salehjg/AINGF2/FPGA_Side/ipcore_dir/icon1.v

///////////////////////////////////////////////////////////////////////////////
// Copyright (c) 2015 Xilinx, Inc.
// All Rights Reserved
///////////////////////////////////////////////////////////////////////////////
//   ____  ____
//  /   /\/   /
// /___/  \  /    Vendor     : Xilinx
// \   \   \/     Version    : 14.7
//  \   \         Application: Xilinx CORE Generator
//  /   /         Filename   : icon1.v
// /___/   /\     Timestamp  : Wed Nov 25 22:33:35 Iran Standard Time 2015
// \   \  /  \
//  \___\/\___\
//
// Design Name: Verilog Synthesis Wrapper
///////////////////////////////////////////////////////////////////////////////
// This wrapper is used to integrate with Project Navigator and PlanAhead

`timescale 1ns/1ps

module icon1(
    CONTROL0) /* synthesis syn_black_box syn_noprune=1 */;


inout [35 : 0] CONTROL0;

endmodule
