salehjg/AINGF2/FPGA_Side/ipcore_dir/ila1/example_design/example_ila1.v

//////////////////////////////////////////////////////////////////////////////
//$Date: 2012/02/06 10:34:16 $
//$RCSfile: example_design.ejava,v $
//$Revision: 1.4 $
///////////////////////////////////////////////////////////////////////////////
//   ____  ____ 
//  /   /\/   /
// /___/  \  /    Vendor: Xilinx
// \   \   \/     Version : 1.05
//  \   \         Application : ILA V1.05a
//  /   /         Filename : example_ila1.v
// /___/   /\     
// \   \  /  \ 
//  \___\/\___\
//
// (c) Copyright 2010 Xilinx, Inc. All rights reserved.
// 
// This file contains confidential and proprietary information
// of Xilinx, Inc. and is protected under U.S. and
// international copyright and other intellectual property
// laws.
// 
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
// CRITICAL APPLICATIONS
// Xilinx products are not designed or intended to be fail-
// safe, or for use in any application requiring fail-safe
// performance, such as life-support or safety devices or
// systems, Class III medical devices, nuclear facilities,
// applications related to the deployment of airbags, or any
// other applications that could lead to death, personal
// injury, or severe property or environmental damage
// (individually and collectively, "Critical
// Applications"). Customer assumes the sole risk and
// liability of any use of Xilinx products in Critical
// Applications, subject only to applicable laws and
// regulations governing limitations on product liability.
// 
// THIS COPYRIGHT NOTICE AND DISCLAIMER MUST BE RETAINED AS
// PART OF THIS FILE AT ALL TIMES.

`timescale 1ns / 1ps

//The example module here illustrates how ila core can be instantiated in
//a user design. This helps the user on how various ports selected for the core can be used.

module example_ila1
  (
 
    input         clk_i); 
  //****************************************************************************
  //  Local Parameters
  //****************************************************************************
  parameter C_NUM_OF_TRIGPORTS = 2;
  parameter C_TRIG0_SIZE = 20;
  parameter C_TRIG1_SIZE = 1;


  //****************************************************************************
  //  Local Signals
  //****************************************************************************
  wire clk;
  wire [35:0] control0;
  wire [C_TRIG0_SIZE-1:0] trig_0;
  wire [C_TRIG1_SIZE-1:0] trig_1;
  wire [C_NUM_OF_TRIGPORTS:0] en_out_int;


   
 
  BUFG bufg_inst
    (
      .O(clk),
      .I(clk_i));
  //-----------------------------------------------------------------
  //
  //  For TRIG0
  //
  //-----------------------------------------------------------------
  // This shift register takes enable_in and registers enable_out. Size of 
  // shift register is given as TRIG0 width. Output of shift register 
  // is mapped to TRIG0.en_out of this shift_reg instance can be used as
  // en_in for next shift_reg instance. 

  // Enabling First shift register

  assign en_out_int[0] = 1'b1;

  shift_reg
    #(.WIDTH(C_TRIG0_SIZE))
    U_SHIFT_REGISTER_0
      (
       .clk(clk),
       .en_in(en_out_int[0]),
       .en_out(en_out_int[1]),
       .shiftout(trig_0));

  //-----------------------------------------------------------------
  //
  //  For TRIG1
  //
  //-----------------------------------------------------------------
  // This shift register takes enable_in from the previous shift register and 
  // registers enable_out.Size of shift register is given as TRIG1 width.
  // Output of shift register is mapped TRIG1. en_out of this shift_reg 
  // instance can be used as en_in for next shift_reg instance.Each trigger port 
  // in the design can be distinguished by its pulse width.TRIG0 signals 
  // are of shorter width than those of TRIG1.

  shift_reg
    #(.WIDTH(C_TRIG1_SIZE))
    U_SHIFT_REGISTER_1
      (
       .clk(clk),
       .en_in(en_out_int[1]),
       .en_out(en_out_int[2]),
       .shiftout(trig_1));

  //-----------------------------------------------------------------
  //
  //  IF TRIGOUT Port is selected
  //
  //-----------------------------------------------------------------


  //-----------------------------------------------------------------
  //
  //  If Data not same as trigger
  //
  //-----------------------------------------------------------------

  //-----------------------------------------------------------------
  //
  //  ICON Pro core instance
  //
  //-----------------------------------------------------------------
  // Icon core is instantiated to connect to ILA core.
  chipscope_icon ICON_inst 
    (
      .CONTROL0(control0)); // INOUT BUS [35:0]


  //-----------------------------------------------------------------
  //
  //  ILA Pro core instance
  //
  //-----------------------------------------------------------------
  // When this design is run on analyzer, shift operation is observed on each trigger port.
  // The pulse width is different for any two trigger ports. If Data port is selected, 
  // Johnson Counter operation can be observed on Data port. If Trig_out port is selected,
  // shift operation can be viewed on VIO core. 



  ila1 ILA_inst 
    (
      .CONTROL(control0), // INOUT BUS [35:0]
      .CLK(clk), // IN
      .TRIG0(trig_0), // IN BUS [19:0] 
      .TRIG1(trig_1)); // IN BUS [0:0] 


endmodule

//-------------------------------------------------------------------
//
//  Shift Register module
//
//-------------------------------------------------------------------
// Shift register module is a ring counter logic along with en_in and en_out. 
// This logic generates walking one pattern of given width when en_in is '1'. 
// en_out is MSB of the shiftout. Width of shift register is parameterized 
// and default width is specified as '8'. If the width is '1', toggle pattern is generated.

module shift_reg
 #(parameter WIDTH = 8) 
  (
    input clk,
    input en_in,
    output en_out,
    output [WIDTH-1:0] shiftout);

  reg [WIDTH-1:0] val;
  initial 
  val = 'b1;
  reg en_out_reg;
  

  assign shiftout = val;
  
  // One shot enable
  assign en_out = (val[WIDTH-1] && !(en_out_reg));

  // Ring Counter logic
  generate
    if (WIDTH > 1)
      begin : if_name
        always@(posedge clk) begin
    	  if (en_in == 1'b1) begin
      	    val <= {val[WIDTH-2:0],val[WIDTH-1]};
    	  end
  	end
      end
    else
      begin : else_name
        always@(posedge clk) begin
          if (en_in == 1'b1) begin
            val <= !val;
          end
        end
      end
  endgenerate
 
  // Registering enable out
  always@(posedge clk) begin
    en_out_reg <= val[WIDTH-1];
  end

endmodule
