salehjg/AINGF2/FPGA_Side/ipcore_dir/mc8051_ram/simulation/functional/wave_ncsim.sv

 
 
 




window new WaveWindow  -name  "Waves for BMG Example Design"
waveform  using  "Waves for BMG Example Design"

      waveform add -signals /mc8051_ram_tb/status
      waveform add -signals /mc8051_ram_tb/mc8051_ram_synth_inst/bmg_port/CLKA
      waveform add -signals /mc8051_ram_tb/mc8051_ram_synth_inst/bmg_port/ADDRA
      waveform add -signals /mc8051_ram_tb/mc8051_ram_synth_inst/bmg_port/DINA
      waveform add -signals /mc8051_ram_tb/mc8051_ram_synth_inst/bmg_port/WEA
      waveform add -signals /mc8051_ram_tb/mc8051_ram_synth_inst/bmg_port/ENA
      waveform add -signals /mc8051_ram_tb/mc8051_ram_synth_inst/bmg_port/DOUTA

console submit -using simulator -wait no "run"
